ErickMorales1312/Proyecto-IMTC/Unit Test/GPS/Motores_GPS/HTML.h

#ifndef HTML_h
#define HTML_h

#include <Arduino.h>

extern bool State2;
extern bool State1;
extern bool State0;
extern float Longitud;
extern float Latitud; 
extern float HDOP;
extern int Satellites; 

String SendHTML(uint8_t Status2, uint8_t Status1, uint8_t Status0);
String generateButtonHTML(uint8_t Status2, uint8_t Status1, uint8_t Status0);

#endif
